valentintintin/arduino-tracker-aprs-dra818/src/GPS.h

#ifndef ARDUINO_TRACKER_APRS_DRA818_GPS_H
#define ARDUINO_TRACKER_APRS_DRA818_GPS_H

#include <Arduino.h>
#include <TinyGPS++.h>
#include <SoftwareSerial.h>

#define TIME_WAIT_DATA 1000

class GPS {
public:
    explicit GPS(byte rxPin, int baud = 9600, byte txPin = 0);

    bool getData();

    void displayInfo();

    TinyGPSPlus gps;
private:
    SoftwareSerial *serial;

    int baud;
};


#endif //ARDUINO_TRACKER_APRS_DRA818_GPS_H
